cscott/OpenEVSE_Keypad_RFID/Tester/include/cap1214-reg.h

#define CAP1214_I2C_ADDR (0x50>>1)

#define CAP1214_REG_MAIN_STATUS		0x00
#define CAP1214_REG_BUTTON_STATUS_1	0x03
#define CAP1214_REG_BUTTON_STATUS_2	0x04
#define CAP1214_REG_BUILD_REVISION	0x05
#define CAP1214_REG_SLIDER_POSITION	0x06
#define CAP1214_REG_VENDOR_ID		0x08
#define CAP1214_REG_VOLUMETRIC_STEP	0x09
#define CAP1214_REG_NOISE_STATUS_1	0x0A
#define CAP1214_REG_NOISE_STATUS_2	0x0B
#define CAP1214_REG_LID_CLOSURE_STATUS_1 0x0C
#define CAP1214_REG_LID_CLOSURE_STATUS_2 0x0D
#define CAP1214_REG_GPIO_STATUS		0x0E
#define CAP1214_REG_GROUP_STATUS	0x0F
#define CAP1214_REG_SENSOR_1_DELTA_COUNT 0x10
#define CAP1214_REG_SENSOR_2_DELTA_COUNT 0x11
#define CAP1214_REG_SENSOR_3_DELTA_COUNT 0x12
#define CAP1214_REG_SENSOR_4_DELTA_COUNT 0x13
#define CAP1214_REG_SENSOR_5_DELTA_COUNT 0x14
#define CAP1214_REG_SENSOR_6_DELTA_COUNT 0x15
#define CAP1214_REG_SENSOR_7_DELTA_COUNT 0x16
#define CAP1214_REG_SENSOR_8_DELTA_COUNT 0x17
#define CAP1214_REG_SENSOR_9_DELTA_COUNT 0x18
#define CAP1214_REG_SENSOR_10_DELTA_COUNT 0x19
#define CAP1214_REG_SENSOR_11_DELTA_COUNT 0x1A
#define CAP1214_REG_SENSOR_12_DELTA_COUNT 0x1B
#define CAP1214_REG_SENSOR_13_DELTA_COUNT 0x1C
#define CAP1214_REG_SENSOR_14_DELTA_COUNT 0x1D
#define CAP1214_REG_QUEUE_CONTROL	0x1E
#define CAP1214_REG_DATA_SENSITIVITY	0x1F
#define CAP1214_REG_CONFIGURATION	0x20
#define CAP1214_REG_SENSOR_ENABLE	0x21
#define CAP1214_REG_BUTTON_CONFIGURATION 0x22
#define CAP1214_REG_GROUP_CONFIGURATION_1 0x23
#define CAP1214_REG_GROUP_CONFIGURATION_2 0x24
#define CAP1214_REG_CALIBRATION_ENABLE	0x25
#define CAP1214_REG_CALIBRATION_ACTIVATE 0x26
#define CAP1214_REG_INTERRUPT_ENABLE_1	0x27
#define CAP1214_REG_INTERRUPT_ENABLE_2	0x28
#define CAP1214_REG_SLEEP_CHANNEL_CONTROL 0x29
#define CAP1214_REG_MULTIPLE_PRESS_CONFIGURATION 0x2A
#define CAP1214_REG_LID_CLOSURE_CONFIGURATION 0x2B
#define CAP1214_REG_LID_CLOSURE_QUEUE_CONTROL 0x2C
#define CAP1214_REG_LID_CLOSURE_PATTERN_1 0x2D
#define CAP1214_REG_LID_CLOSURE_PATTERN_2 0x2E
#define CAP1214_REG_RECALIBRATION_CONFIGURATION 0x2F
#define CAP1214_REG_SENSOR_1_THRESHOLD	0x30
#define CAP1214_REG_SENSOR_2_THRESHOLD	0x31
#define CAP1214_REG_SENSOR_3_THRESHOLD	0x32
#define CAP1214_REG_SENSOR_4_THRESHOLD	0x33
#define CAP1214_REG_SENSOR_5_THRESHOLD	0x34
#define CAP1214_REG_SENSOR_6_THRESHOLD	0x35
#define CAP1214_REG_SENSOR_7_THRESHOLD	0x36
#define CAP1214_REG_GROUP_THRESHOLD	0x37
#define CAP1214_REG_BUTTON_NOISE_THRESHOLD_1 0x38
#define CAP1214_REG_BUTTON_NOISE_THRESHOLD_2 0x39
#define CAP1214_REG_LID_CLOSURE_THRESHOLD_1 0x3A
#define CAP1214_REG_LID_CLOSURE_THRESHOLD_2 0x3B
#define CAP1214_REG_LID_CLOSURE_THRESHOLD_3 0x3C
#define CAP1214_REG_LID_CLOSURE_THRESHOLD_4 0x3D
#define CAP1214_REG_SLIDE_VELOCITY_CONFIGURATION 0x3E
#define CAP1214_REG_DIGITAL_RECALIBRATION 0x3F
#define CAP1214_REG_CONFIGURATION_2	0x40
#define CAP1214_REG_GROUPED_CHANNEL_SENSOR_ENABLE 0x41
#define CAP1214_REG_PROXIMITY_CONTROL	0x42
#define CAP1214_REG_GROUPED_SENSOR_CALIBRATION_ACTIVATE 0x46
#define CAP1214_REG_SAMPLING_CHANNEL_SELECT 0x4E
#define CAP1214_REG_SAMPLING_CONFIGURATION 0x4F
#define CAP1214_REG_SENSOR_1_BASE_COUNT	0x50
#define CAP1214_REG_SENSOR_2_BASE_COUNT	0x51
#define CAP1214_REG_SENSOR_3_BASE_COUNT	0x52
#define CAP1214_REG_SENSOR_4_BASE_COUNT	0x53
#define CAP1214_REG_SENSOR_5_BASE_COUNT	0x54
#define CAP1214_REG_SENSOR_6_BASE_COUNT	0x55
#define CAP1214_REG_SENSOR_7_BASE_COUNT	0x56
#define CAP1214_REG_SENSOR_8_BASE_COUNT	0x57
#define CAP1214_REG_SENSOR_9_BASE_COUNT	0x58
#define CAP1214_REG_SENSOR_10_BASE_COUNT	0x59
#define CAP1214_REG_SENSOR_11_BASE_COUNT	0x5A
#define CAP1214_REG_SENSOR_12_BASE_COUNT	0x5B
#define CAP1214_REG_SENSOR_13_BASE_COUNT	0x5C
#define CAP1214_REG_SENSOR_14_BASE_COUNT	0x5D
#define CAP1214_REG_LED_STATUS_1	0x60
#define CAP1214_REG_LED_STATUS_2	0x61
#define CAP1214_REG_FEEDBACK_CONFIGURATION 0x62
#define CAP1214_REG_FEEDBACK_CHANNEL_CONFIGURATION_1 0x63
#define CAP1214_REG_FEEDBACK_CHANNEL_CONFIGURATION_2 0x64
#define CAP1214_REG_FEEDBACK_ONESHOT	0x65
#define CAP1214_REG_LED_GPIO_DIRECTION	0x70
#define CAP1214_REG_LED_GPIO_OUTPUT_TYPE 0x71
#define CAP1214_REG_GPIO_INPUT		0x72
#define CAP1214_REG_LED_OUTPUT_CONTROL_1 0x73
#define CAP1214_REG_LED_OUTPUT_CONTROL_2 0x74
#define CAP1214_REG_LED_POLARITY_1	0x75
#define CAP1214_REG_LED_POLARITY_2	0x76
#define CAP1214_REG_LINKED_LED_TRANSITION_CONTROL_1 0x77
#define CAP1214_REG_LINKED_LED_TRANSITION_CONTROL_2 0x78
#define CAP1214_REG_LED_MIRROR_CONTROL_1 0x79
#define CAP1214_REG_LED_MIRROR_CONTROL_2 0x7A
#define CAP1214_REG_SENSOR_LED_LINKING	0x80
#define CAP1214_REG_LED_BEHAVIOR_1	0x81
#define CAP1214_REG_LED_BEHAVIOR_2	0x82
#define CAP1214_REG_LED_BEHAVIOR_3	0x83
#define CAP1214_REG_LED_PULSE_1_PERIOD	0x84
#define CAP1214_REG_LED_PULSE_2_PERIOD	0x85
#define CAP1214_REG_LED_BREATHE_PERIOD	0x86
#define CAP1214_REG_LED_CONFIGURATION	0x88
#define CAP1214_REG_LED11_CONFIGURATION	0x8A
#define CAP1214_REG_LED_PULSE_1_DUTY_CYCLE 0x90
#define CAP1214_REG_LED_PULSE_2_DUTY_CYCLE 0x91
#define CAP1214_REG_LED_BREATHE_DUTY_CYCLE 0x92
#define CAP1214_REG_LED_DIRECT_DUTY_CYCLE 0x93
#define CAP1214_REG_LED_DIRECT_RAMP_RATES 0x94
#define CAP1214_REG_LED_OFF_DELAY	0x95
#define CAP1214_REG_SENSOR_1_CALIBRATION 0xB1
#define CAP1214_REG_SENSOR_2_CALIBRATION 0xB2
#define CAP1214_REG_SENSOR_3_CALIBRATION 0xB3
#define CAP1214_REG_SENSOR_4_CALIBRATION 0xB4
#define CAP1214_REG_SENSOR_5_CALIBRATION 0xB5
#define CAP1214_REG_SENSOR_6_CALIBRATION 0xB6
#define CAP1214_REG_SENSOR_7_CALIBRATION 0xB7
#define CAP1214_REG_SENSOR_8_CALIBRATION 0xB8
#define CAP1214_REG_SENSOR_9_CALIBRATION 0xB9
#define CAP1214_REG_SENSOR_10_CALIBRATION 0xBA
#define CAP1214_REG_SENSOR_11_CALIBRATION 0xBB
#define CAP1214_REG_SENSOR_12_CALIBRATION 0xBC
#define CAP1214_REG_SENSOR_13_CALIBRATION 0xBD
#define CAP1214_REG_SENSOR_14_CALIBRATION 0xBE
#define CAP1214_REG_SENSOR_1_CALIBRATION_LOW 0xD0
#define CAP1214_REG_SENSOR_5_CALIBRATION_LOW 0xD1
#define CAP1214_REG_SENSOR_9_CALIBRATION_LOW 0xD2
#define CAP1214_REG_SENSOR_13_CALIBRATION_LOW 0xD3
#define CAP1214_REG_PRODUCT_ID		0xFD
#define CAP1214_REG_MANUFACTURER_ID	0xFE
#define CAP1214_REG_REVISION		0xFF
